solo-fsw/timing_tester/Hardware/Firmware/TimingTester/TimingtesterStandalone/timingtester.h

//Hw
#define MARKEROUT 4
#define MARKER_INT 3  //Int0
#define LIGHTSENSOR_INT 2  //Int1
#define SOUND_INT 1  //Int3
#define SRBOX_INT 0  //Int2
#define NOTEST 0
#define DISPLAYTEST 1
#define AUDIOTEST 2
#define SRBOXTEST 3



byte MicroSign[] = { //µ
  B00000,
  B00000,
  B00000,
  B10010,
  B10010,
  B10010,
  B11100,
  B10000

};
